Nicodaube/Grisp_robot/Laptop_controller/img/arrow.png

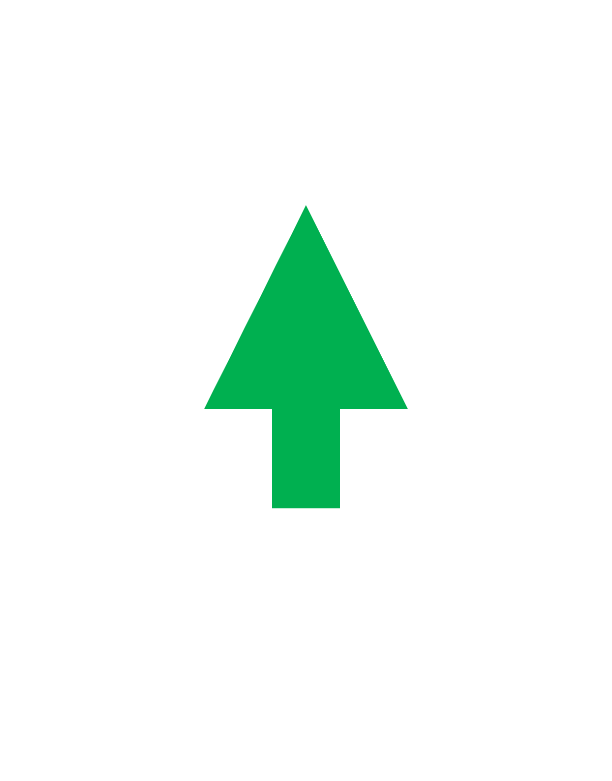
Laptop_controller/img/arrow.png
