Nicodaube/Grisp_robot/Laptop_controller/img/minus.png

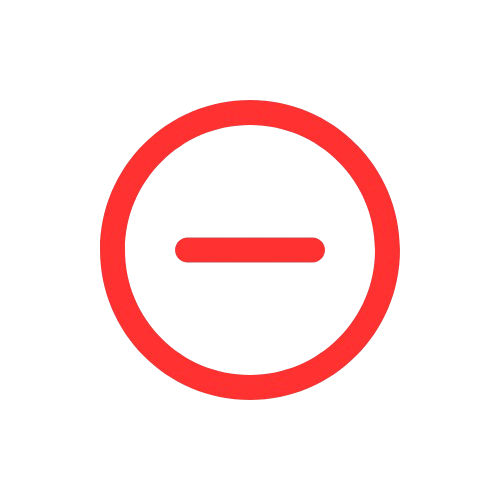
Laptop_controller/img/minus.png
