Nicodaube/Grisp_robot/Laptop_controller/img/plus.png

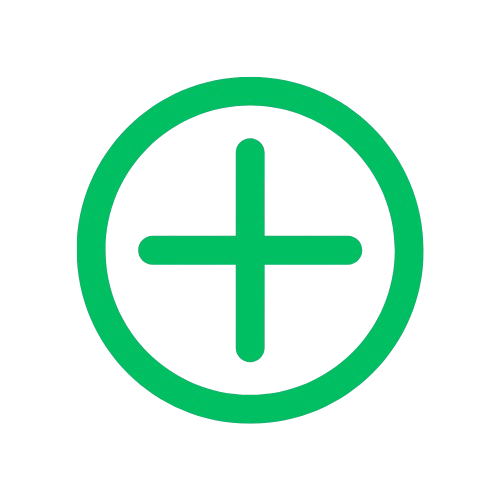
Laptop_controller/img/plus.png
