Nicodaube/Grisp_robot/Laptop_controller/img/Robot.png

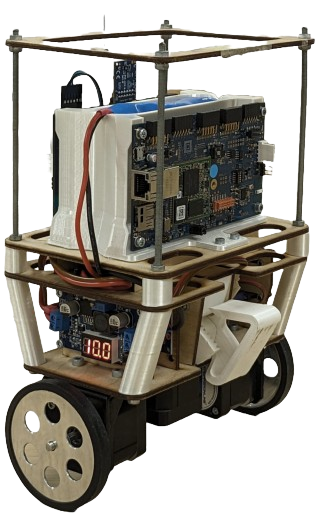
Laptop_controller/img/Robot.png
