Nicodaube/Grisp_robot/Laptop_controller/img/sensor.png

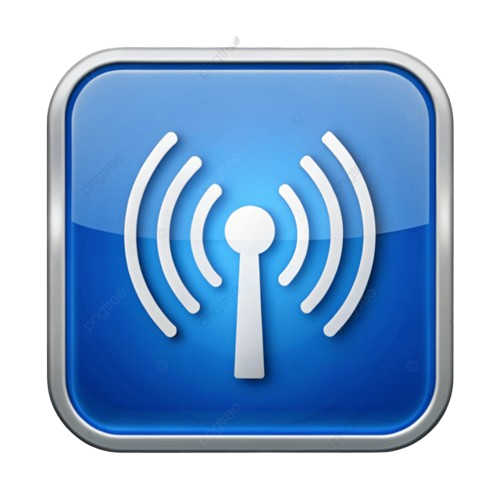
Laptop_controller/img/sensor.png
