Nicodaube/Grisp_robot/Laptop_controller/img/Stop_sign.png

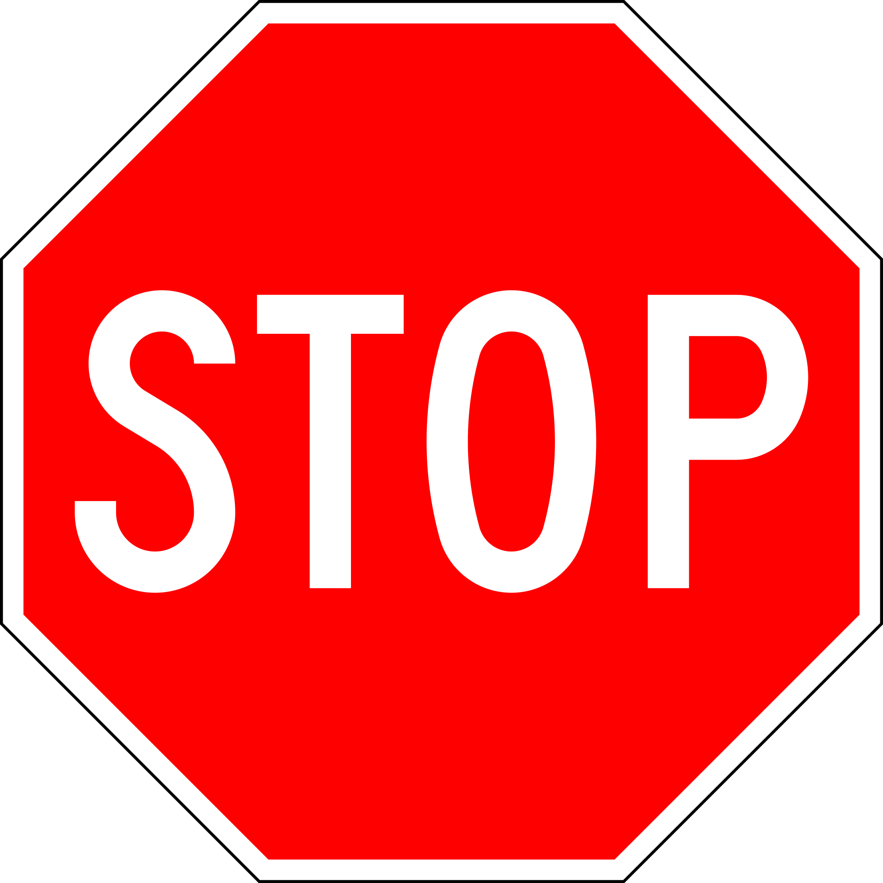
Laptop_controller/img/Stop_sign.png
