Nicodaube/Grisp_robot/Laptop_controller/img/zoom_in.png

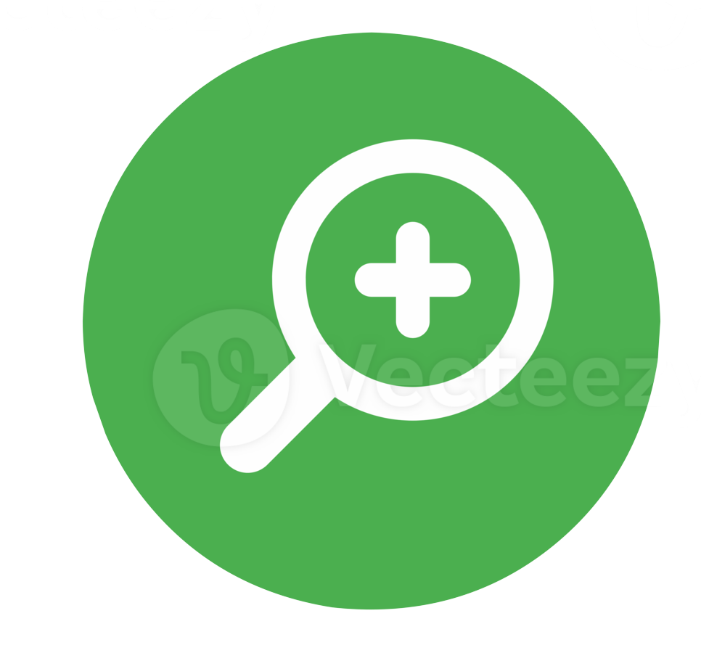
Laptop_controller/img/zoom_in.png
