Nicodaube/Grisp_robot/Laptop_controller/img/zoom_out.png

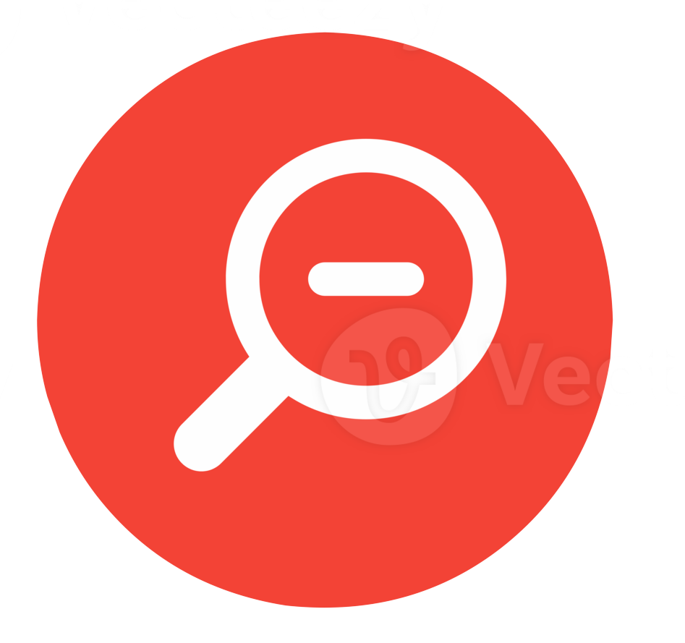
Laptop_controller/img/zoom_out.png
