Nicodaube/Grisp_robot/Wiki_images/GIFS/add_room.gif

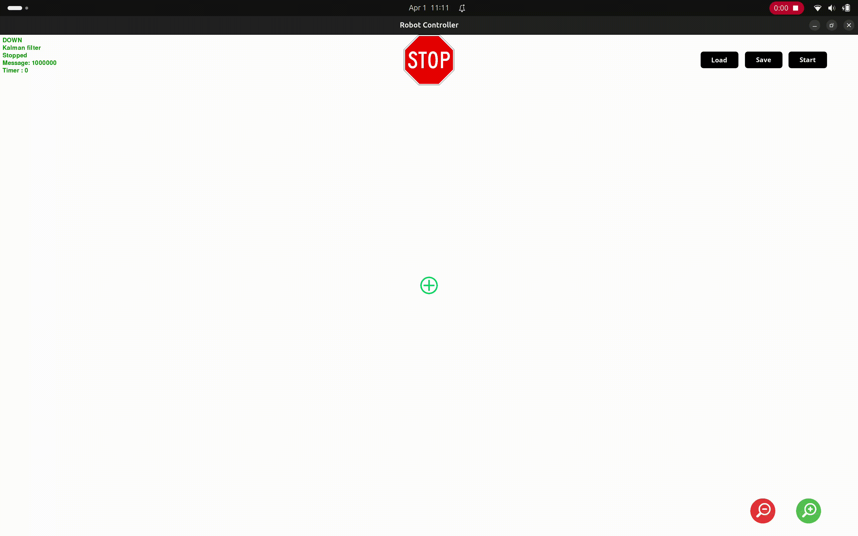
Wiki_images/GIFS/add_room.gif
