Nicodaube/Grisp_robot/Wiki_images/GIFS/add_sens.gif

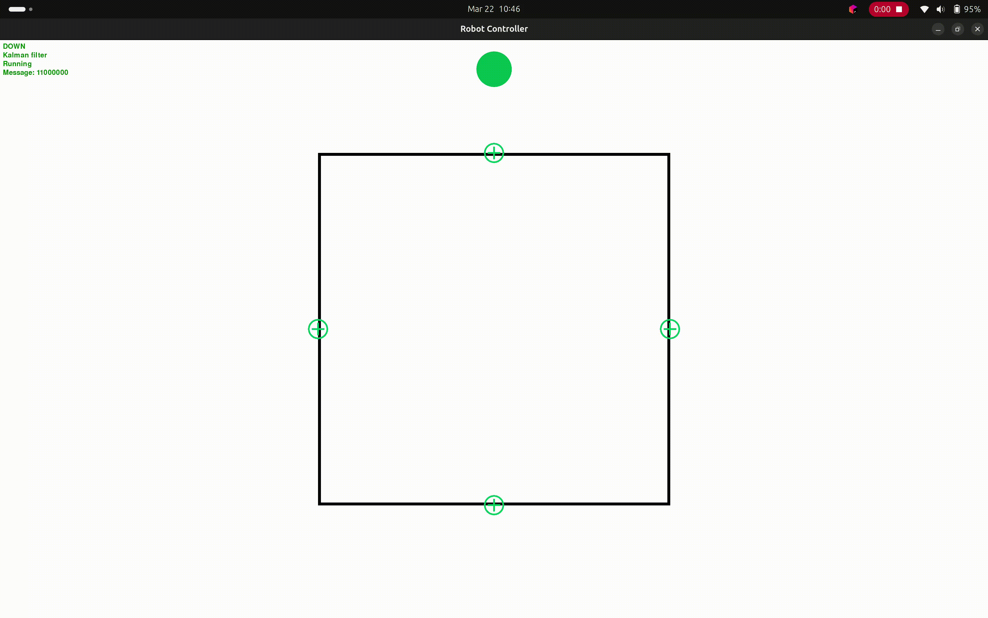
Wiki_images/GIFS/add_sens.gif
