Nicodaube/Grisp_robot/Wiki_images/GIFS/max_compat.gif

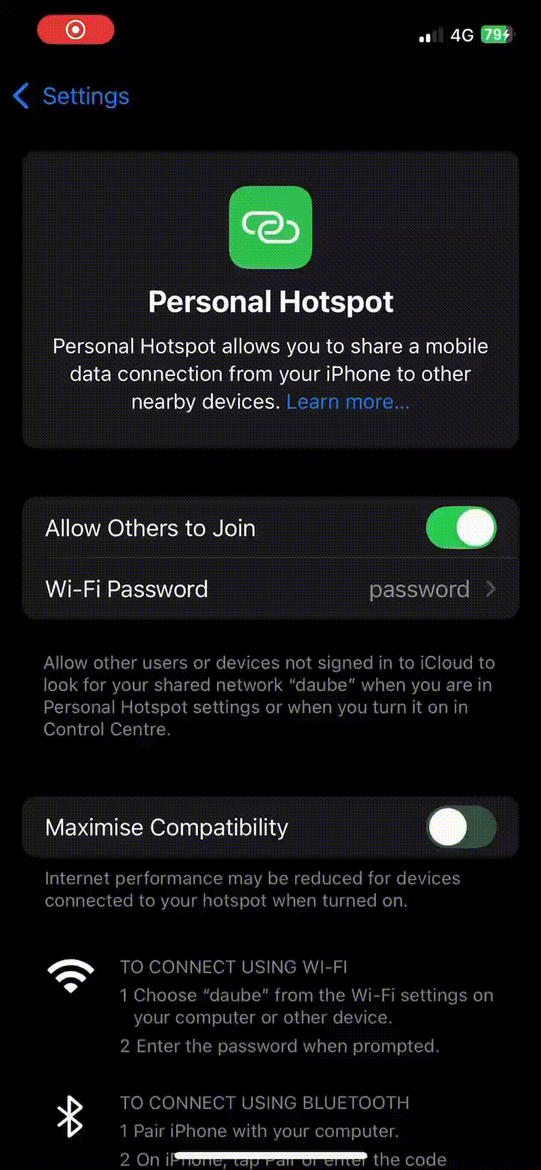
Wiki_images/GIFS/max_compat.gif
