Nicodaube/Grisp_robot/Wiki_images/GIFS/move_ctrl.gif

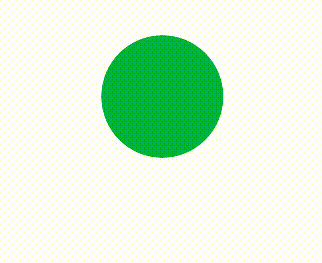
Wiki_images/GIFS/move_ctrl.gif
