Nicodaube/Grisp_robot/Wiki_images/img/jumpers.jpg

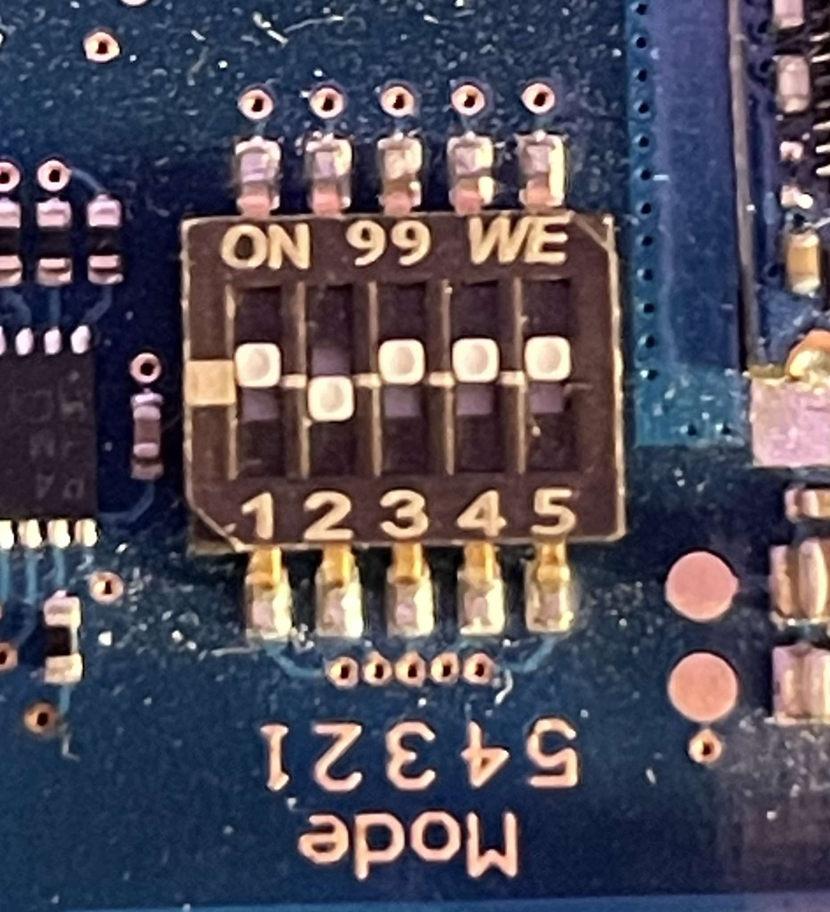
Wiki_images/img/jumpers.jpg
