Nicodaube/Grisp_robot/Wiki_images/img/motor_cables.png

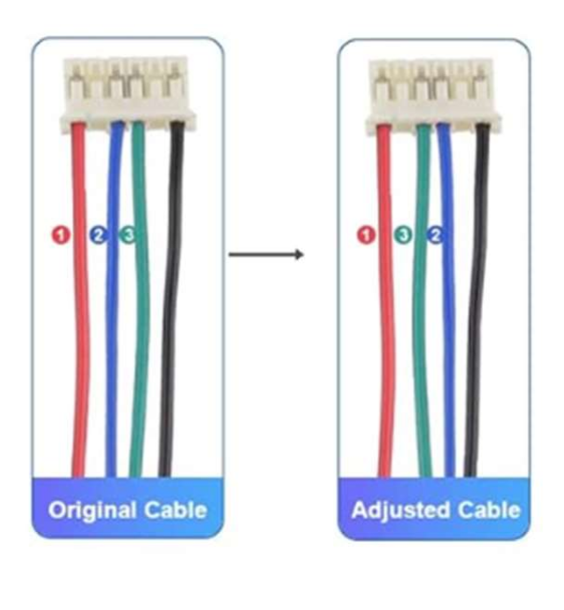
Wiki_images/img/motor_cables.png
