Nicodaube/Grisp_robot/Wiki_images/img/network_config.png

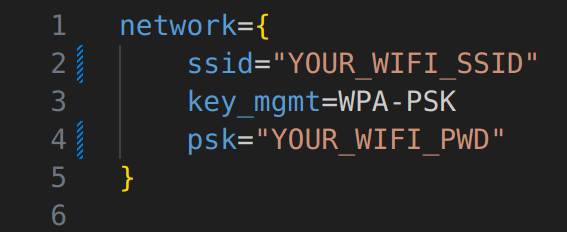
Wiki_images/img/network_config.png
