Nicodaube/Grisp_robot/Wiki_images/img/PCB.png

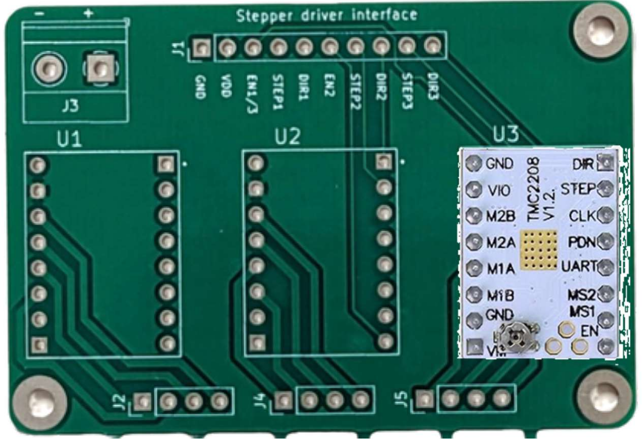
Wiki_images/img/PCB.png
