Nicodaube/Grisp_robot/Wiki_images/img/Sensor.jpeg

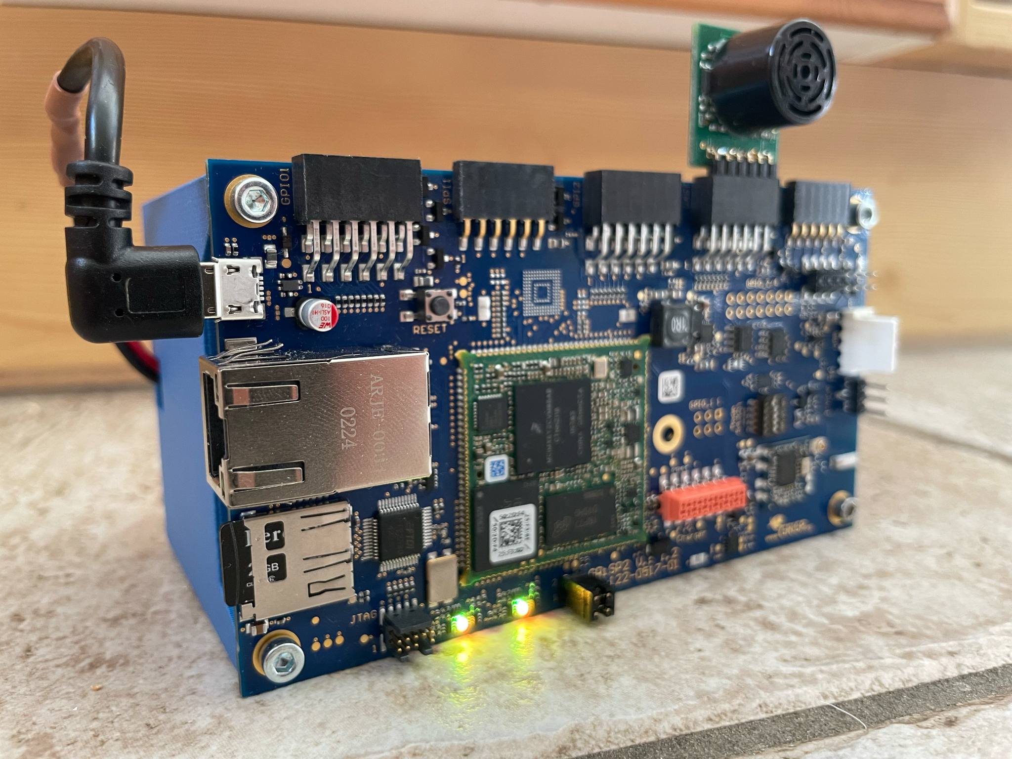
Wiki_images/img/Sensor.jpeg
