Nicodaube/Grisp_robot/Wiki_images/img/Sensor_FSM.png

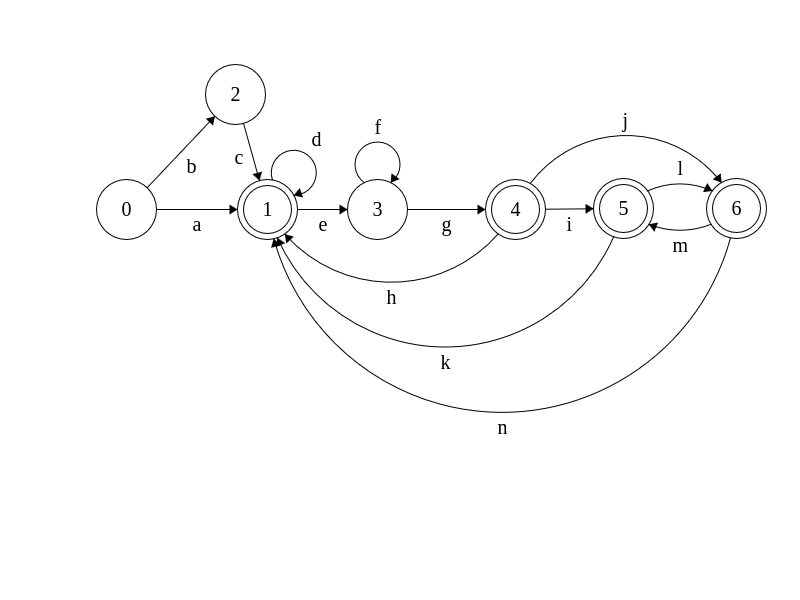
Wiki_images/img/Sensor_FSM.png
