Nicodaube/Grisp_robot/Hardware_robot/CAD_robot/Bevel_rack.SLDPRT

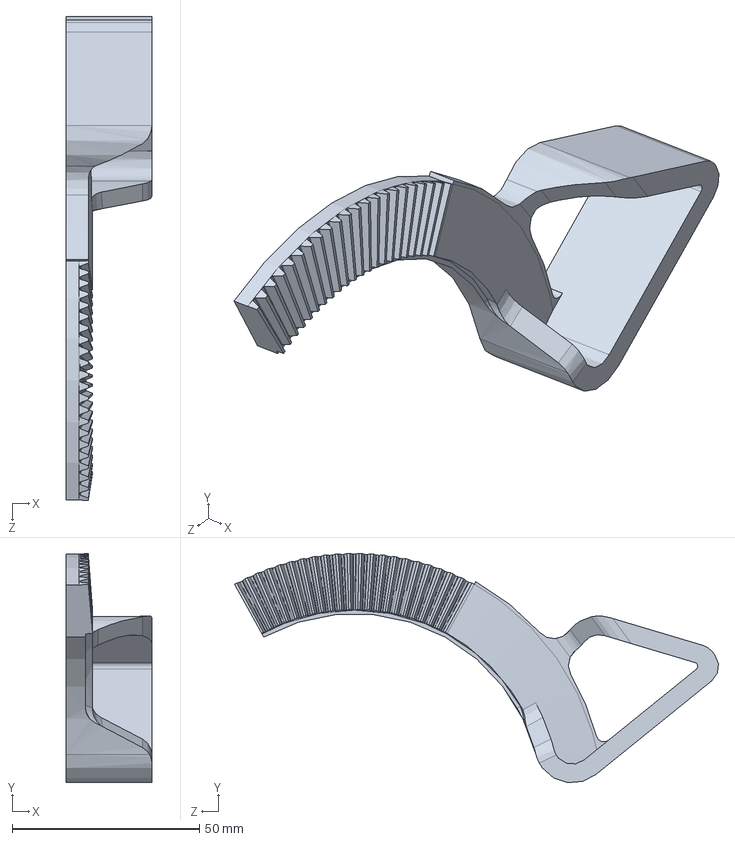
[picture p34: CAD file, 2025-02-24]
Hardware_robot/CAD_robot/Bevel_rack.SLDPRT
23.0 x 61.2 x 129.1 mm
