Nicodaube/Grisp_robot/Hardware_robot/Printing_files/3D/Dx2.STL

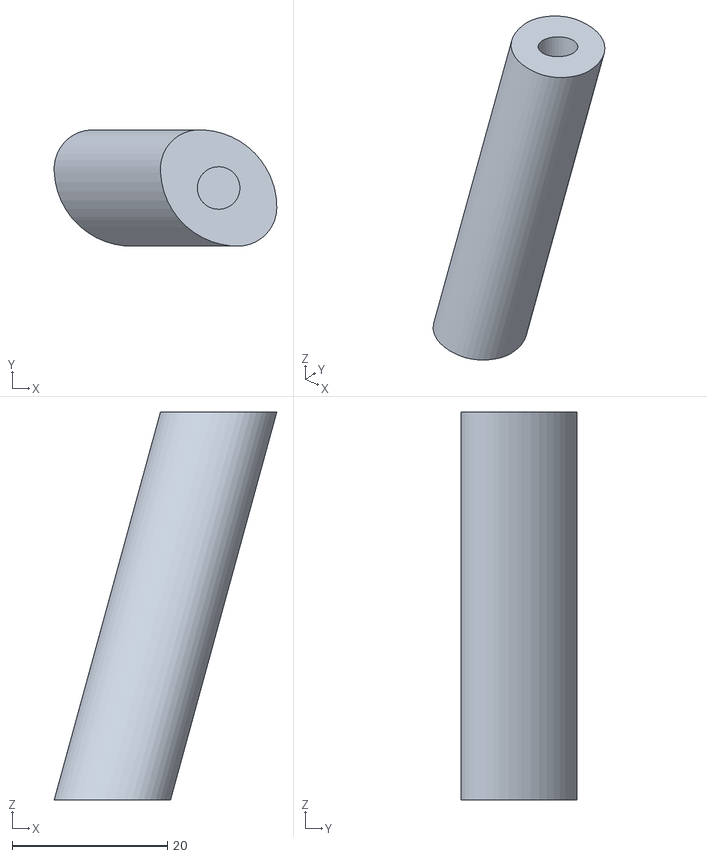
[picture p35: CAD file, 2025-02-23]
Hardware_robot/Printing_files/3D/Dx2.STL
28.7 x 15.0 x 50.0
