Nicodaube/Grisp_robot/Hardware_robot/Printing_files/Laser/H.dxf

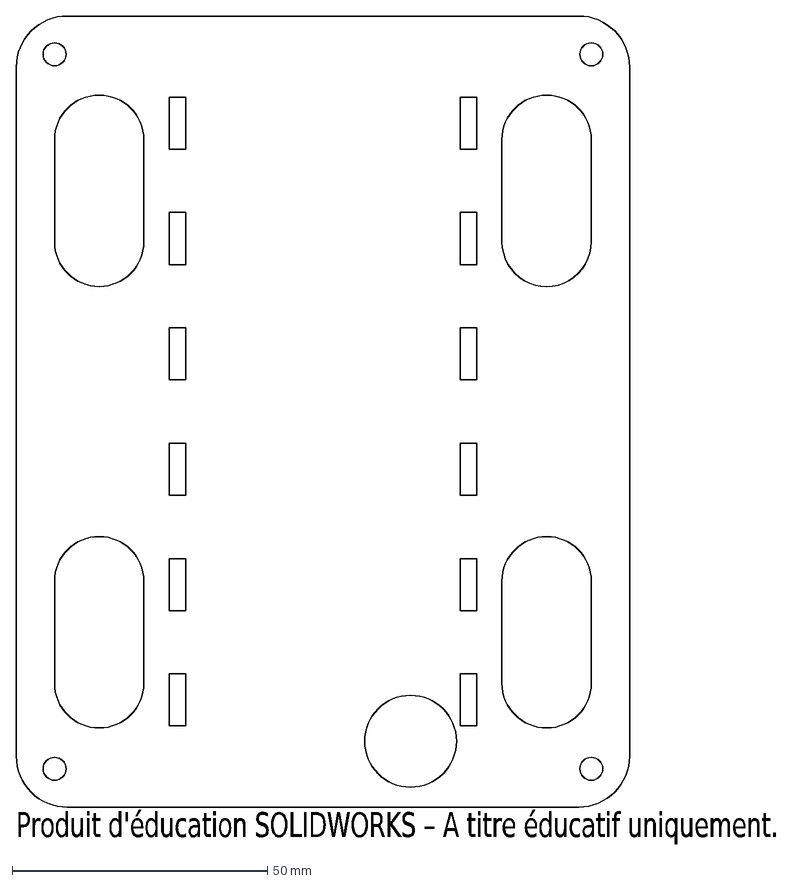
[picture p36: CAD file, 2025-02-23]
Hardware_robot/Printing_files/Laser/H.dxf
Produit d'éducation SOLIDWORKS – A titre éducatif uniquement.
