Nicodaube/Grisp_robot/Hardware_robot/TTGO LORA32 T3 V1.6.1/Wifi_Antenna.step

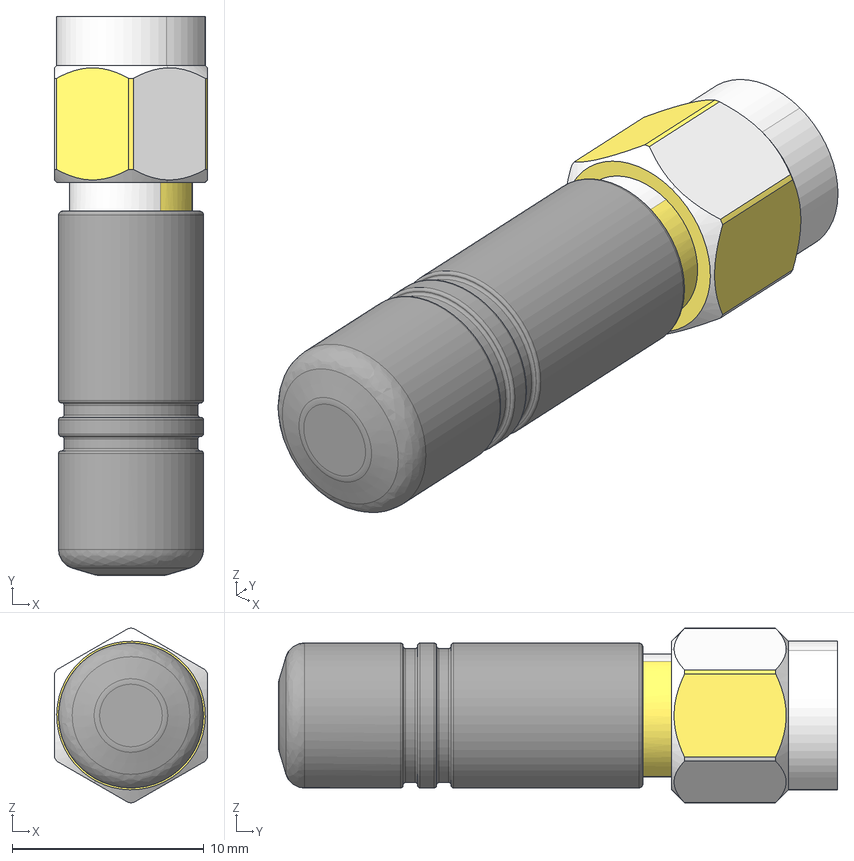
[picture p37: CAD file, 2025-02-24]
Hardware_robot/TTGO LORA32 T3 V1.6.1/Wifi_Antenna.step
8.00 x 29.2 x 9.10 mm
