Nicodaube/Grisp_robot/Hardware_Sensor/3D/Support coin_attache v2.stl

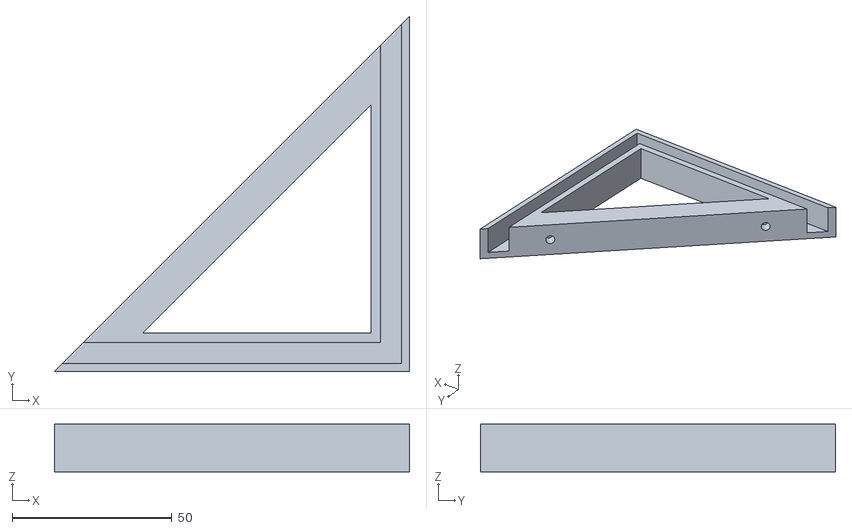
[picture p38: CAD file, 2025-04-22]
Hardware_Sensor/3D/Support coin_attache v2.stl
111.0 x 111.0 x 15.0
