Nicodaube/Grisp_robot/Hardware_robot/Printing_files/3D/G.STL

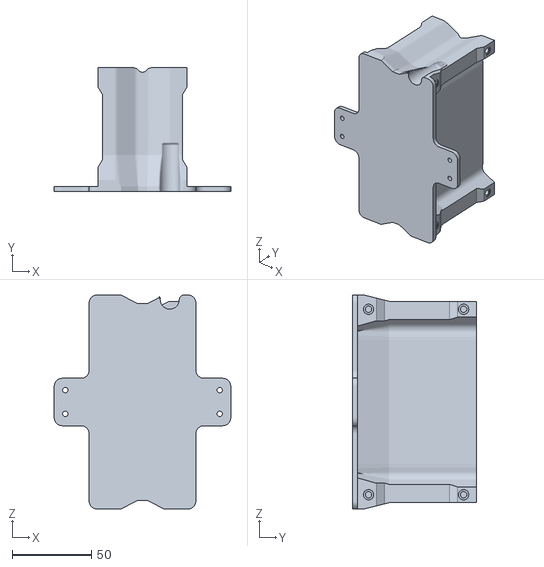
[picture p39: CAD file, 2025-02-23]
Hardware_robot/Printing_files/3D/G.STL
111.4 x 78.0 x 135.0
