Nicodaube/Grisp_robot/Hardware_robot/Printing_files/Laser/D.DXF

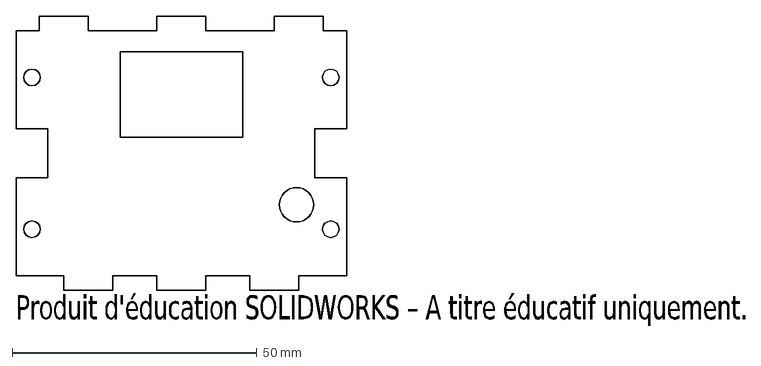
[picture p40: CAD file, 2025-02-23]
Hardware_robot/Printing_files/Laser/D.DXF
Produit d'éducation SOLIDWORKS – A titre éducatif uniquement.
