Nicodaube/Grisp_robot/Hardware_robot/TTGO LORA32 T3 V1.6.1/0603 Green.step

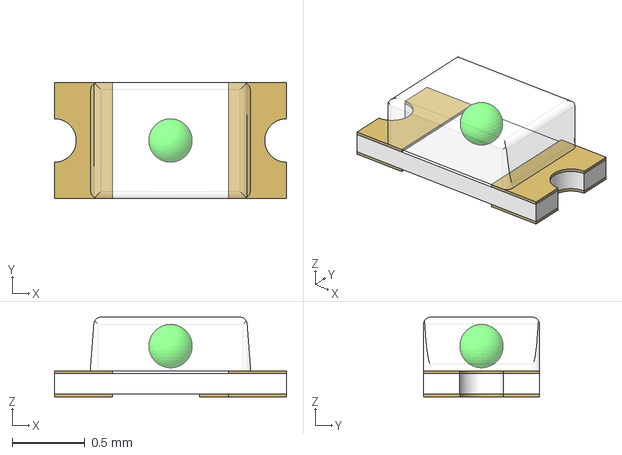
[picture p41: CAD file, 2025-02-24]
Hardware_robot/TTGO LORA32 T3 V1.6.1/0603 Green.step
1.60 x 0.8 x 0.55 mm
