Nicodaube/Grisp_robot/Hardware_robot/CAD_robot/BatteryPackBlue.SLDPRT

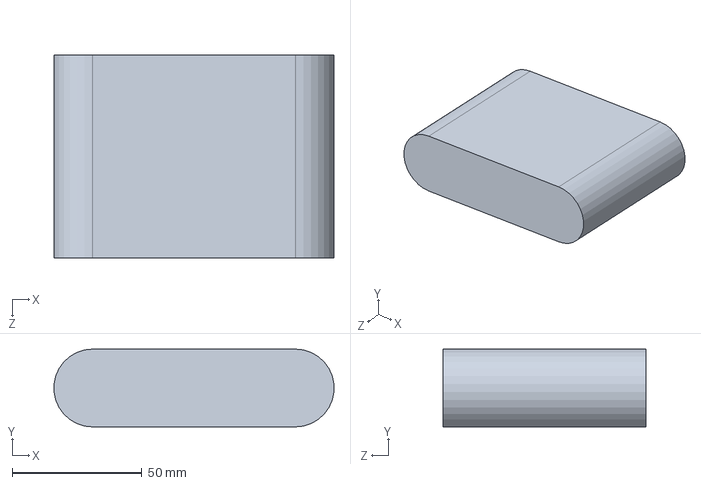
[picture p42: CAD file, 2025-02-24]
Hardware_robot/CAD_robot/BatteryPackBlue.SLDPRT
107.8 x 30.0 x 78.0 mm
