Nicodaube/Grisp_robot/Hardware_robot/Printing_files/3D/B.STL

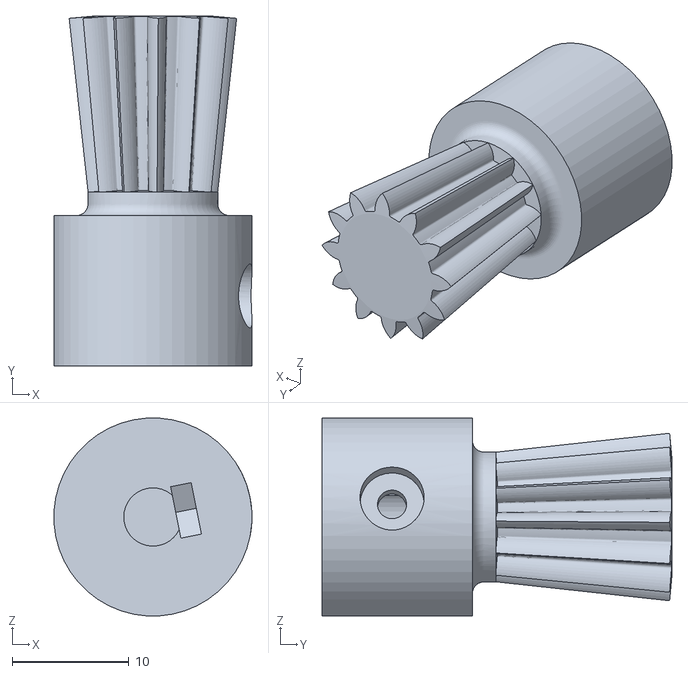
[picture p43: CAD file, 2025-02-23]
Hardware_robot/Printing_files/3D/B.STL
17.0 x 30.0 x 17.0
