Nicodaube/Grisp_robot/Hardware_robot/Printing_files/Laser/C.dxf

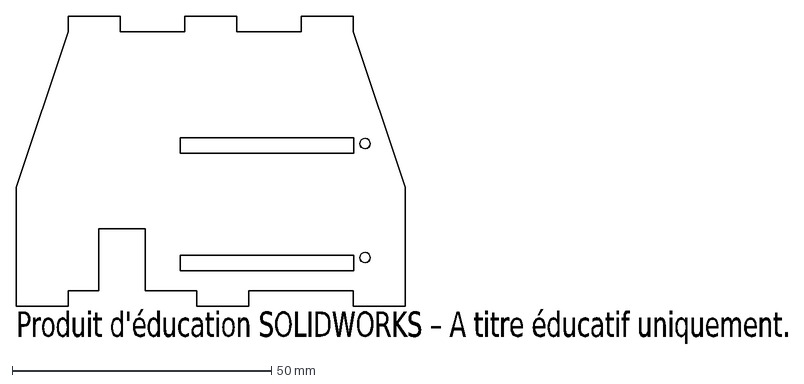
[picture p44: CAD file, 2025-02-23]
Hardware_robot/Printing_files/Laser/C.dxf
Produit d'éducation SOLIDWORKS – A titre éducatif uniquement.
