Nicodaube/Grisp_robot/Hardware_robot/Printing_files/3D/Hx2.STL

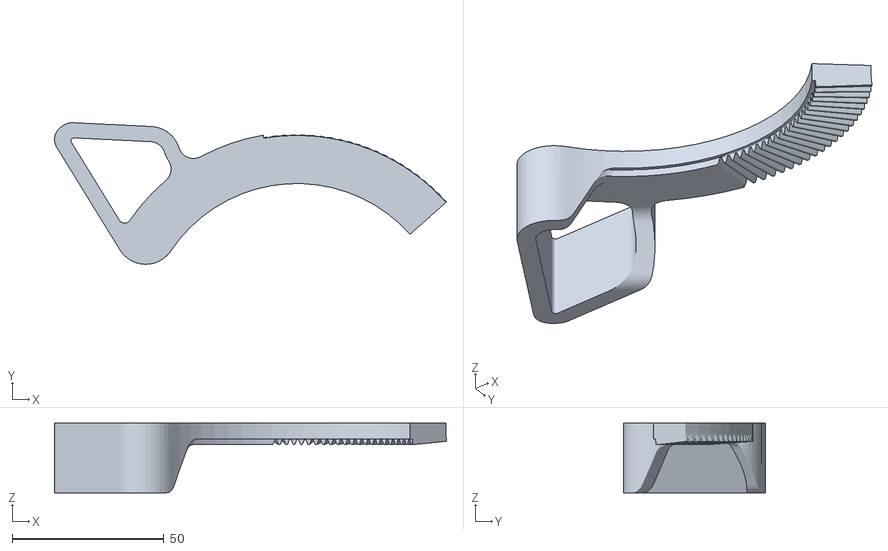
[picture p45: CAD file, 2025-02-23]
Hardware_robot/Printing_files/3D/Hx2.STL
129.4 x 46.8 x 23.0
