Nicodaube/Grisp_robot/Hardware_robot/Printing_files/Laser/Bx2.dxf

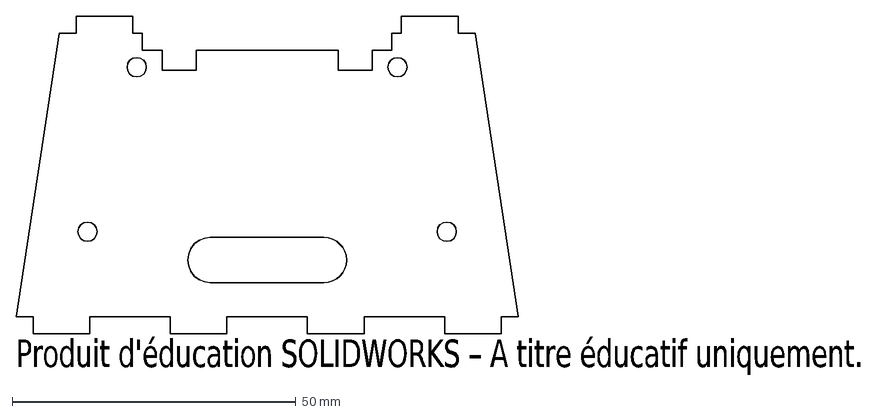
[picture p46: CAD file, 2025-02-23]
Hardware_robot/Printing_files/Laser/Bx2.dxf
Produit d'éducation SOLIDWORKS – A titre éducatif uniquement.
