Nicodaube/Grisp_robot/Hardware_robot/TTGO LORA32 T3 V1.6.1/1TS003B.step

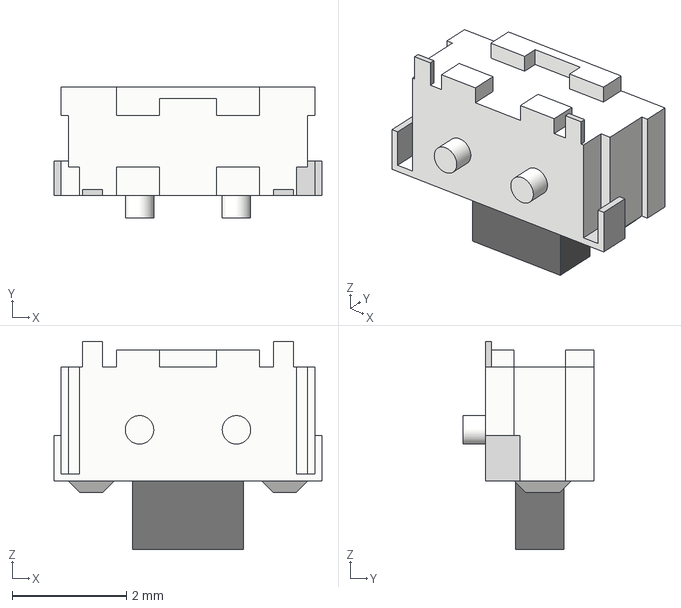
[picture p47: CAD file, 2025-02-24]
Hardware_robot/TTGO LORA32 T3 V1.6.1/1TS003B.step
4.70 x 2.30 x 3.65 mm
