Nicodaube/Grisp_robot/Hardware_robot/Printing_files/Laser/A.dxf

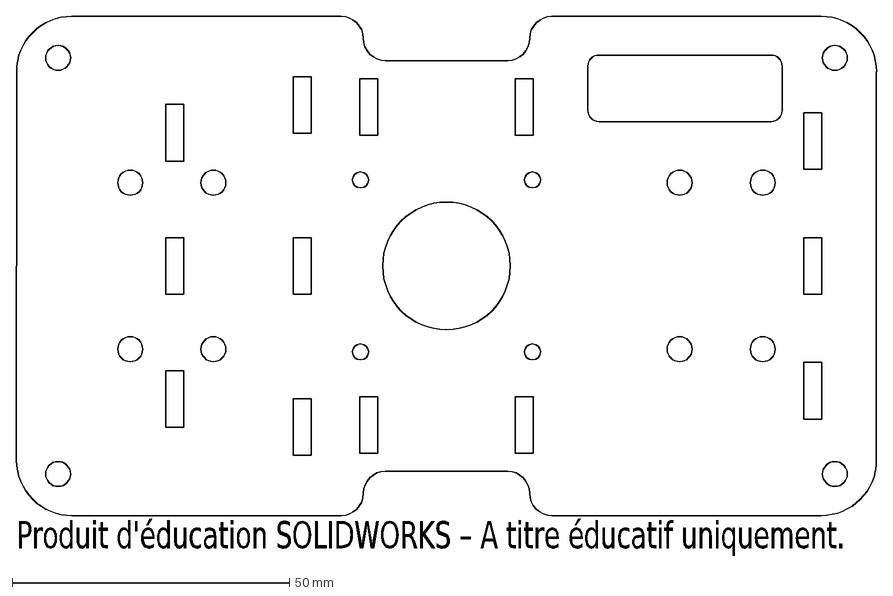
[picture p48: CAD file, 2025-02-23]
Hardware_robot/Printing_files/Laser/A.dxf
Produit d'éducation SOLIDWORKS – A titre éducatif uniquement.
