Nicodaube/Grisp_robot/Hardware_robot/CAD_robot/Pièce20.SLDPRT

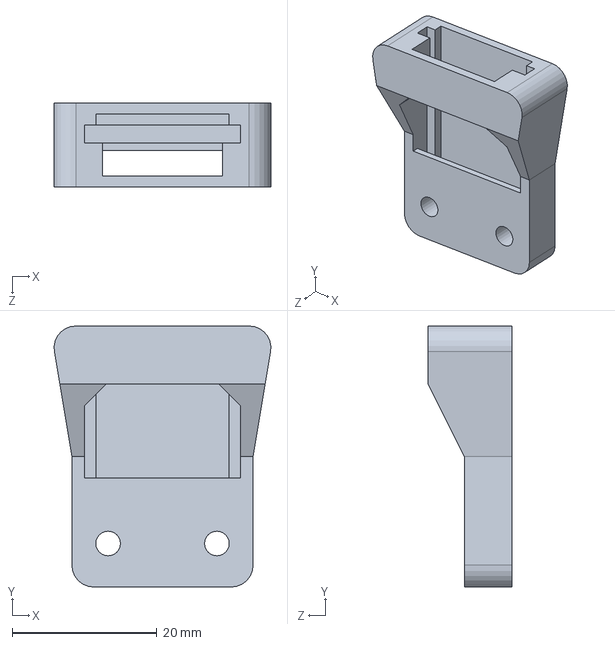
[picture p49: CAD file, 2025-02-24]
Hardware_robot/CAD_robot/Pièce20.SLDPRT
29.9 x 36.0 x 11.6 mm
