Nicodaube/Grisp_robot/Hardware_robot/Printing_files/3D/C.STL

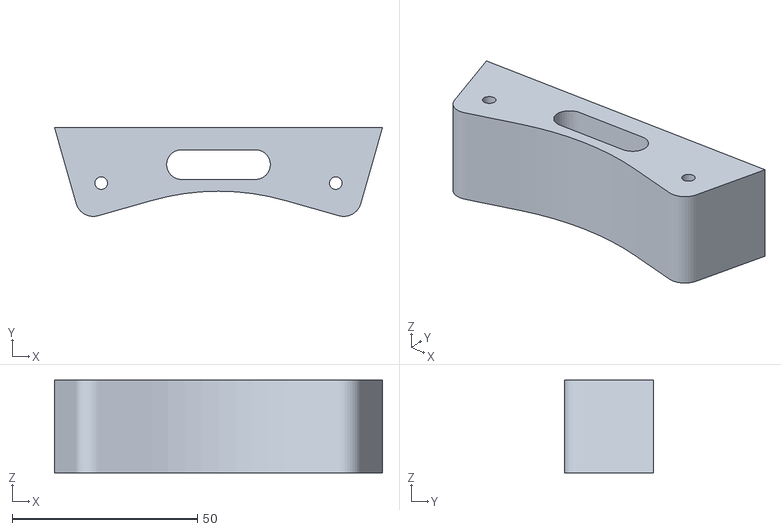
[picture p50: CAD file, 2025-02-23]
Hardware_robot/Printing_files/3D/C.STL
88.6 x 24.0 x 25.0
