Nicodaube/Grisp_robot/Hardware_robot/Printing_files/Laser/Gx2.DXF

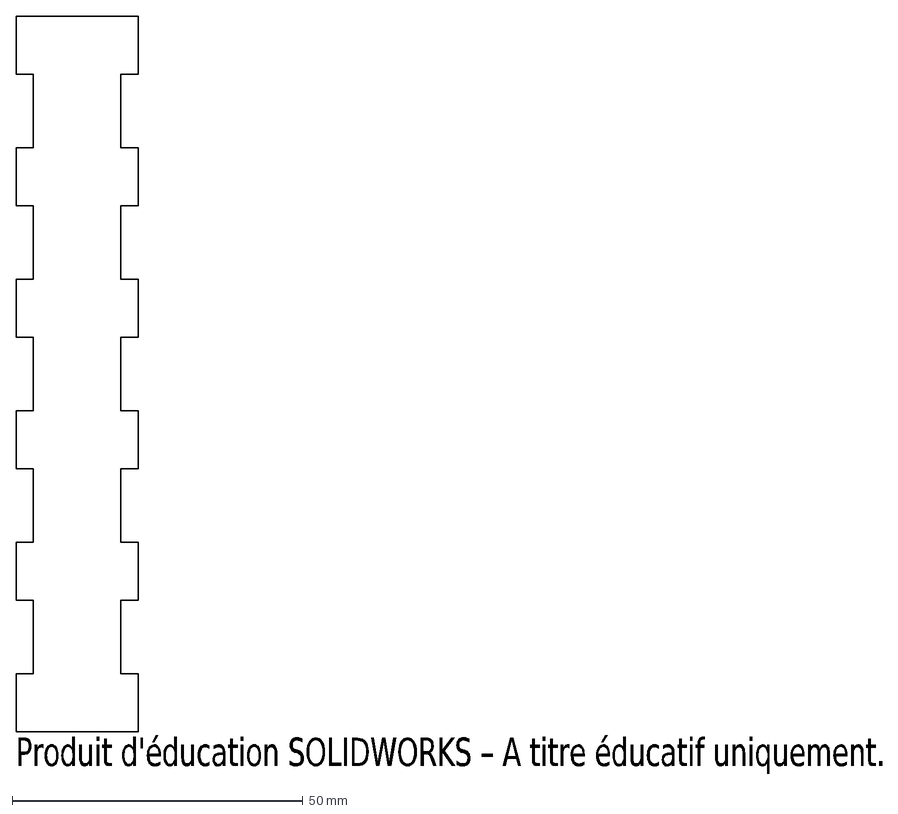
[picture p51: CAD file, 2025-02-23]
Hardware_robot/Printing_files/Laser/Gx2.DXF
Produit d'éducation SOLIDWORKS – A titre éducatif uniquement.
