Nicodaube/Grisp_robot/Hardware_robot/TTGO LORA32 T3 V1.6.1/ESP32-S3-QFN56-77-44.SLDPRT

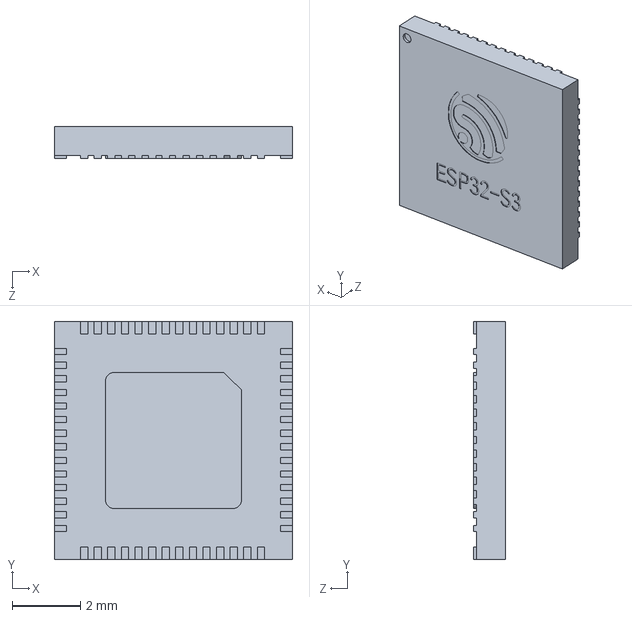
[picture p52: CAD file, 2025-02-24]
Hardware_robot/TTGO LORA32 T3 V1.6.1/ESP32-S3-QFN56-77-44.SLDPRT
7.00 x 7.00 x 0.95 mm
