Nicodaube/Grisp_robot/Hardware_robot/Printing_files/Laser/I.DXF

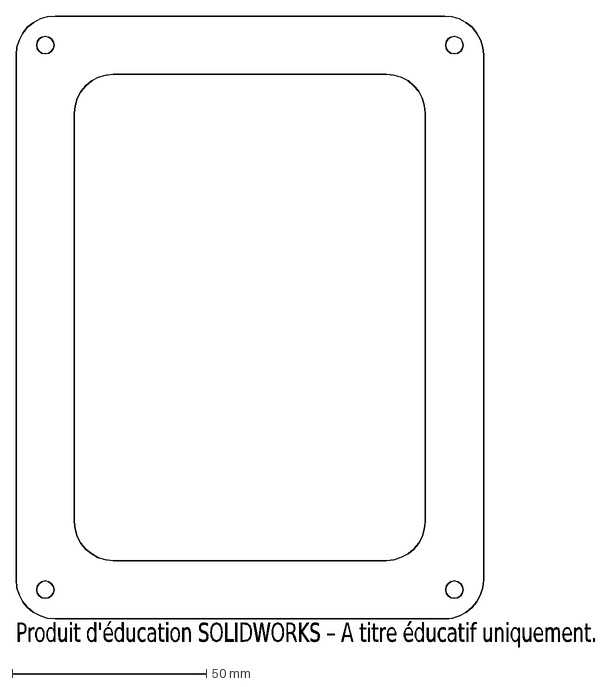
[picture p53: CAD file, 2025-02-23]
Hardware_robot/Printing_files/Laser/I.DXF
Produit d'éducation SOLIDWORKS – A titre éducatif uniquement.
