Nicodaube/Grisp_robot/Hardware_robot/TTGO LORA32 T3 V1.6.1/SMA-angled.SLDPRT

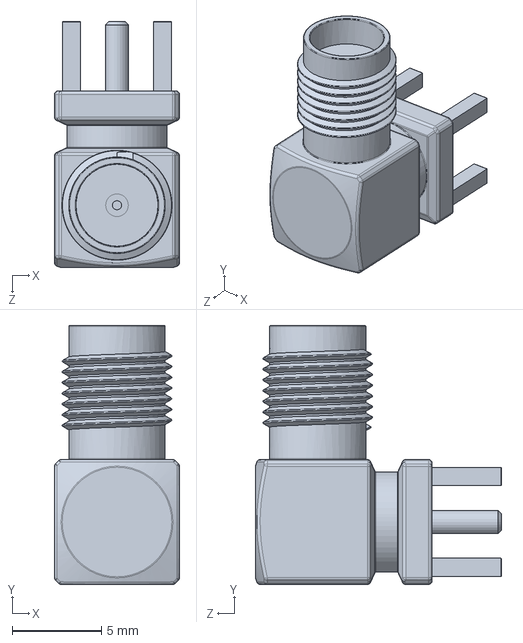
[picture p54: CAD file, 2025-02-24]
Hardware_robot/TTGO LORA32 T3 V1.6.1/SMA-angled.SLDPRT
7.00 x 14.5 x 13.8 mm
