Nicodaube/Grisp_robot/Hardware_robot/TTGO LORA32 T3 V1.6.1/ANT1, PRO-OB-440, M5Stamp-C3.SLDPRT

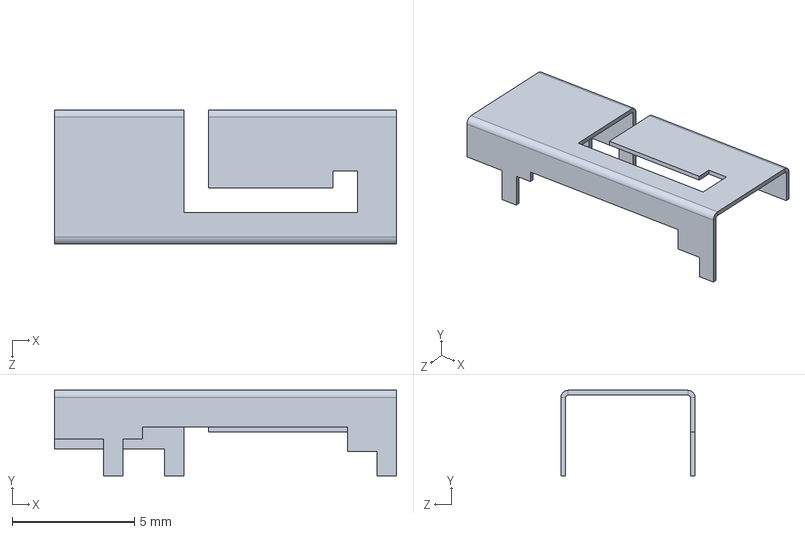
[picture p55: CAD file, 2025-02-24]
Hardware_robot/TTGO LORA32 T3 V1.6.1/ANT1, PRO-OB-440, M5Stamp-C3.SLDPRT
14.0 x 3.50 x 5.50 mm
