Nicodaube/Grisp_robot/Hardware_robot/TTGO LORA32 T3 V1.6.1/PZ_Switch_SMD.stp

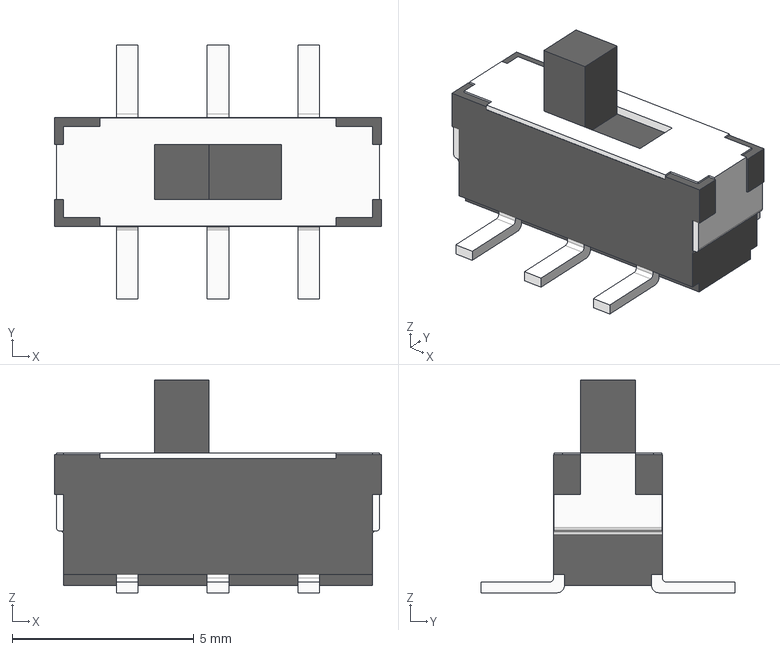
[picture p56: CAD file, 2025-02-24]
Hardware_robot/TTGO LORA32 T3 V1.6.1/PZ_Switch_SMD.stp
9.00 x 7.00 x 5.85 mm
