Nicodaube/Grisp_robot/Hardware_robot/TTGO LORA32 T3 V1.6.1/u.Fl Antenna Connector - 523-A-1JB.SLDPRT

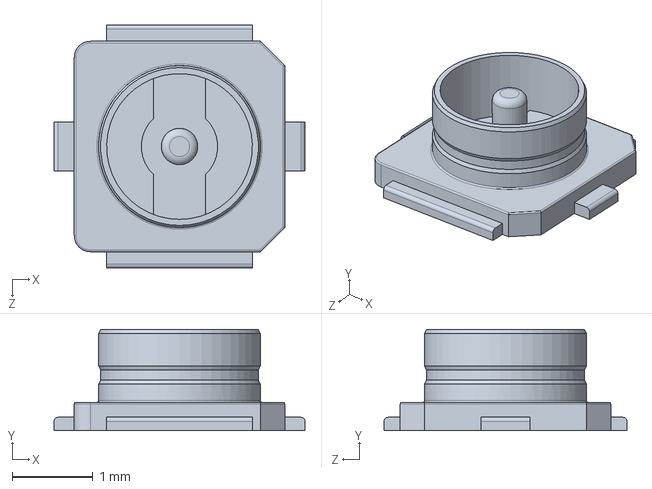
[picture p57: CAD file, 2025-02-24]
Hardware_robot/TTGO LORA32 T3 V1.6.1/u.Fl Antenna Connector - 523-A-1JB.SLDPRT
3.10 x 1.25 x 3.00 mm
