Nicodaube/Grisp_robot/Hardware_robot/TTGO LORA32 T3 V1.6.1/Micro USB-B Female 5Pin SMD.STEP

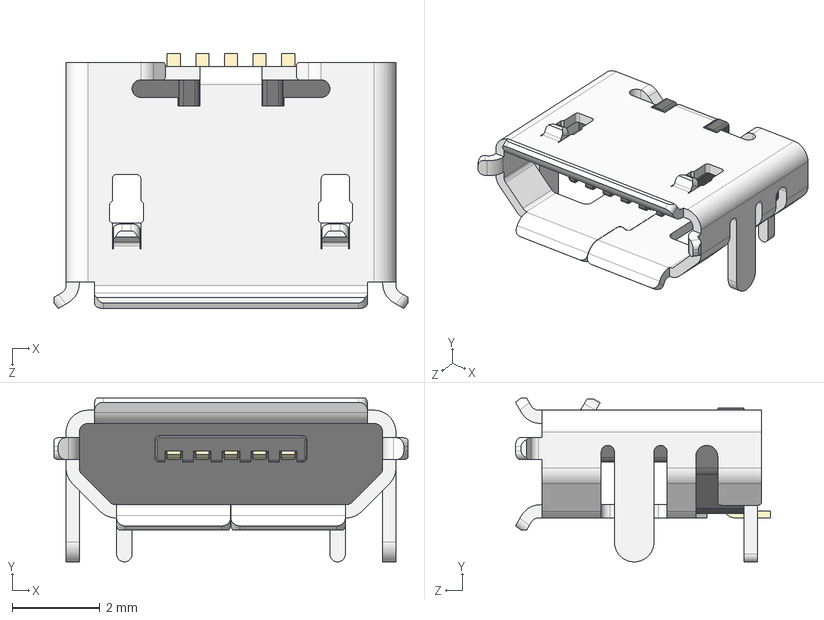
[picture p58: CAD file, 2025-02-24]
Hardware_robot/TTGO LORA32 T3 V1.6.1/Micro USB-B Female 5Pin SMD.STEP
8.05 x 3.73 x 5.80 mm
