Nicodaube/Grisp_robot/Hardware_robot/TTGO LORA32 T3 V1.6.1/Micro SD Card.SLDPRT

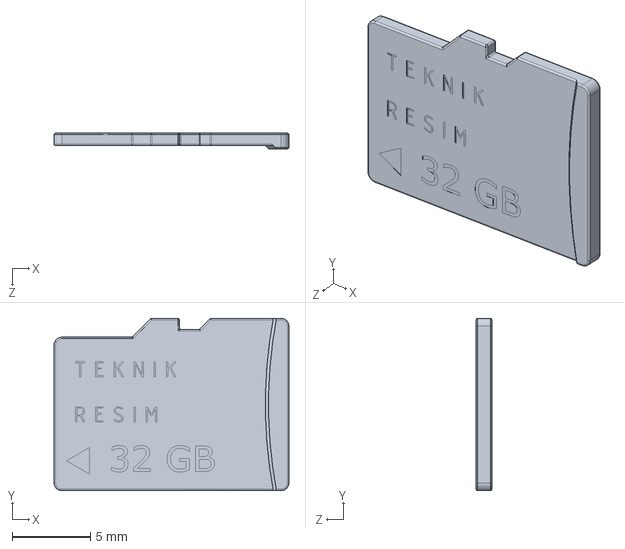
[picture p59: CAD file, 2025-02-24]
Hardware_robot/TTGO LORA32 T3 V1.6.1/Micro SD Card.SLDPRT
15.0 x 11.0 x 1.00 mm
