Nicodaube/Grisp_robot/Hardware_robot/TTGO LORA32 T3 V1.6.1/QFN24(4X4).SLDPRT

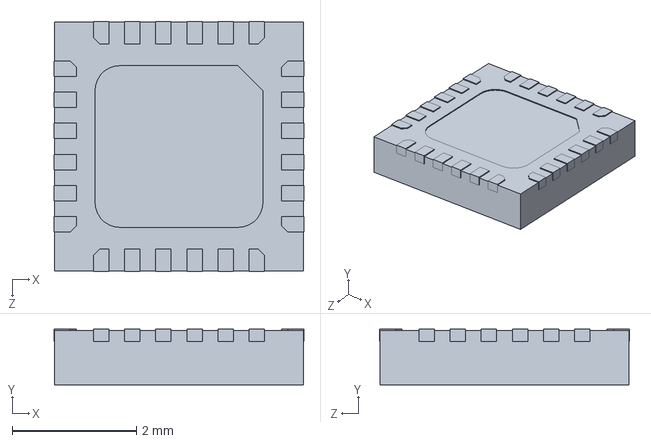
[picture p60: CAD file, 2025-02-24]
Hardware_robot/TTGO LORA32 T3 V1.6.1/QFN24(4X4).SLDPRT
4.02 x 0.9 x 4.02 mm
