Nicodaube/Grisp_robot/Hardware_robot/CAD_robot/17HE15-1504S.STEP

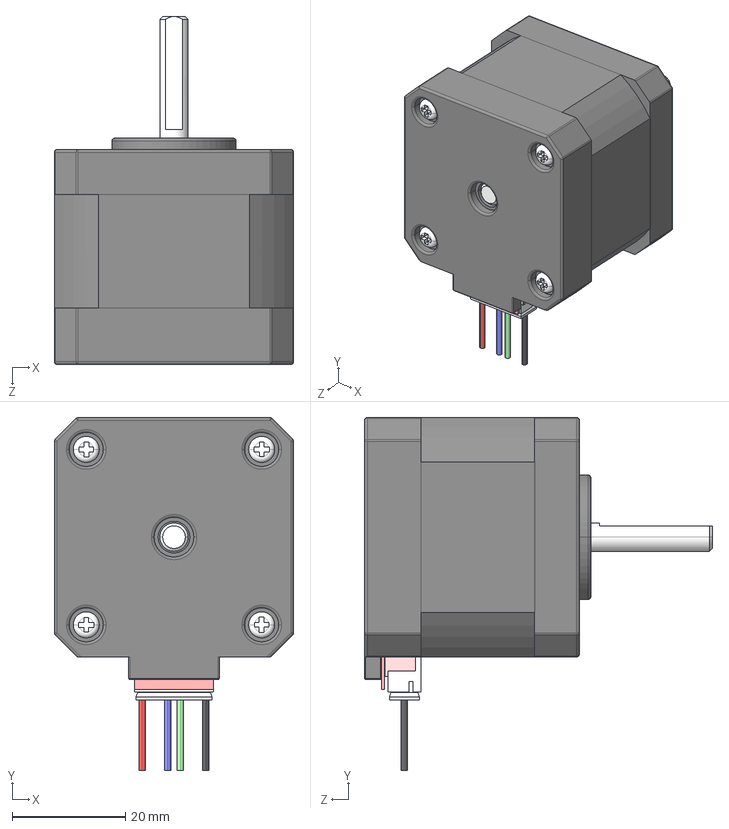
[picture p61: CAD file, 2025-02-24]
Hardware_robot/CAD_robot/17HE15-1504S.STEP
42.3 x 62.4 x 61.5 mm
