Nicodaube/Grisp_robot/Hardware_robot/TTGO LORA32 T3 V1.6.1/pcb lora.SLDPRT

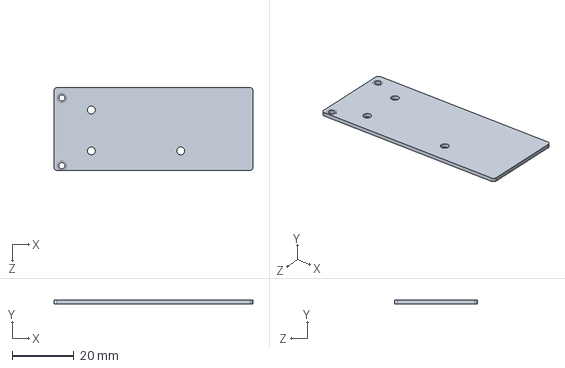
[picture p62: CAD file, 2025-02-24]
Hardware_robot/TTGO LORA32 T3 V1.6.1/pcb lora.SLDPRT
64.7 x 1.18 x 27.0 mm
