Nicodaube/Grisp_robot/Hardware_robot/TTGO LORA32 T3 V1.6.1/OLED block.SLDPRT

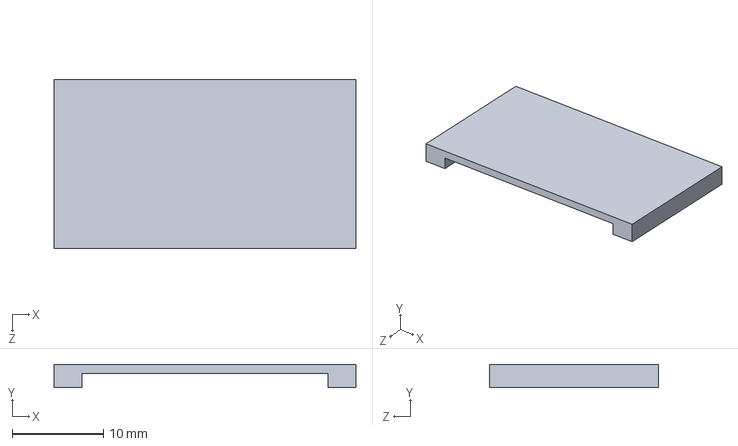
[picture p63: CAD file, 2025-02-24]
Hardware_robot/TTGO LORA32 T3 V1.6.1/OLED block.SLDPRT
33.1 x 2.55 x 18.5 mm
