Nicodaube/Grisp_robot/Hardware_robot/TTGO LORA32 T3 V1.6.1/RFM95 LoRa v15.step

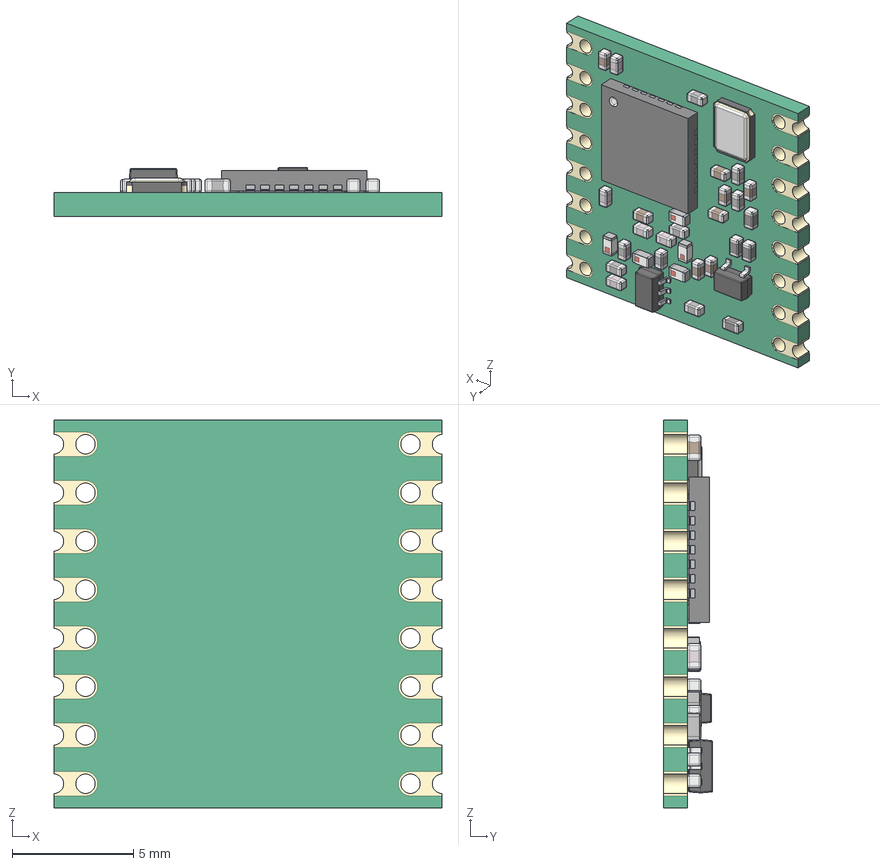
[picture p64: CAD file, 2025-02-24]
Hardware_robot/TTGO LORA32 T3 V1.6.1/RFM95 LoRa v15.step
16.0 x 2.04 x 16.0 mm
QFN 28
SMD Crystal
CAP 0403 x 8
CAP Ceramic 0403 x 8
Res 0403 x 4
CAP ML 0403 x 5
SOT-323
Inductor SMD 0403 x 5
SOT-363
