Nicodaube/Grisp_robot/Hardware_robot/TTGO LORA32 T3 V1.6.1/oled.SLDPRT

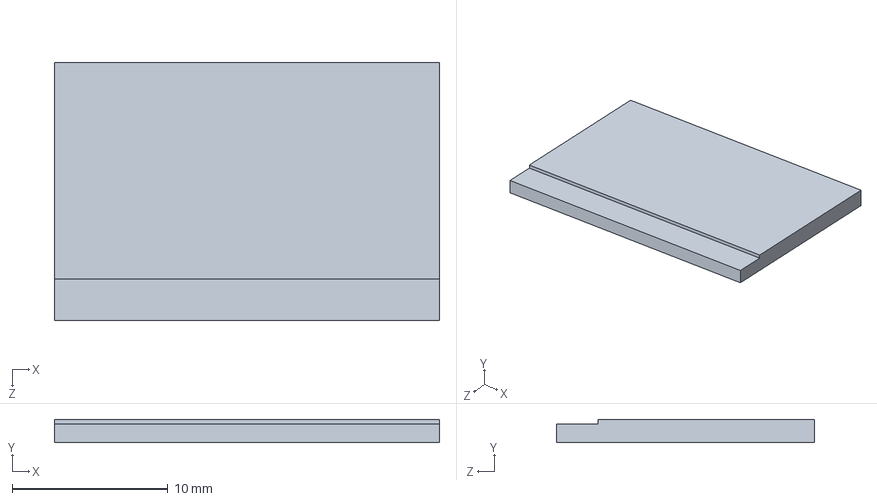
[picture p65: CAD file, 2025-02-24]
Hardware_robot/TTGO LORA32 T3 V1.6.1/oled.SLDPRT
24.7 x 1.50 x 16.6 mm
