Nicodaube/Grisp_robot/Hardware_robot/CAD_robot/BOOST.SLDPRT

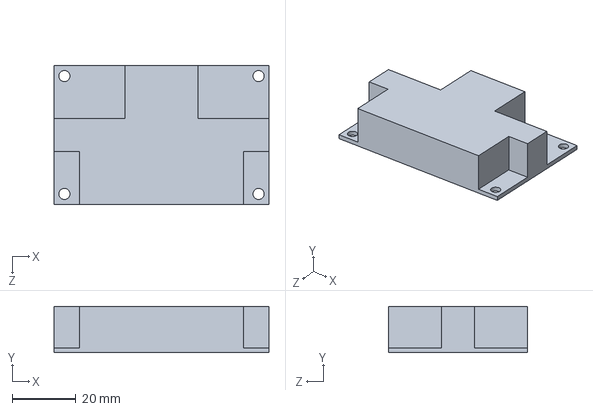
[picture p66: CAD file, 2025-02-24]
Hardware_robot/CAD_robot/BOOST.SLDPRT
67.5 x 14.5 x 43.5 mm
