Nicodaube/Grisp_robot/Hardware_robot/CAD_robot/GRiSP.SLDPRT

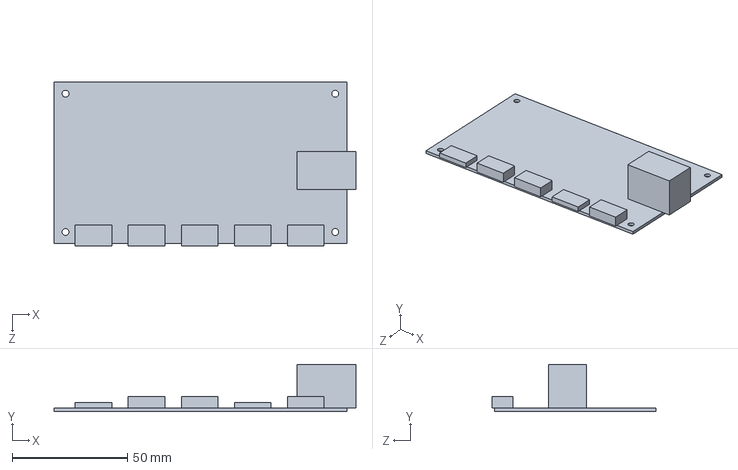
[picture p67: CAD file, 2025-02-24]
Hardware_robot/CAD_robot/GRiSP.SLDPRT
131.0 x 20.5 x 71.0 mm
