Nicodaube/Grisp_robot/Hardware_robot/CAD_robot/CN2596-2.stp

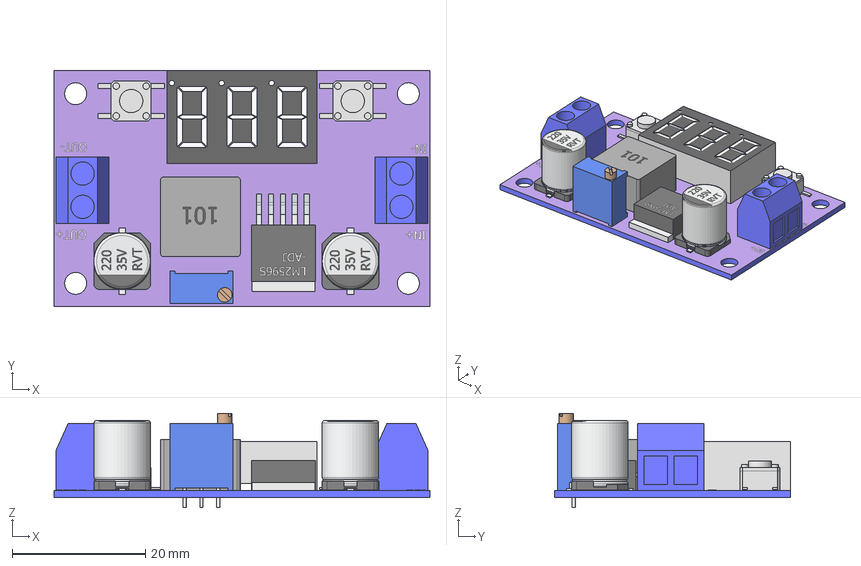
[picture p68: CAD file, 2025-02-24]
Hardware_robot/CAD_robot/CN2596-2.stp
56.5 x 35.5 x 14.2 mm
CN2596-2
LM2596S-ADJ
3631AH-6.8P
PZ_PushButton x 2
Trimpot_3296W
CAPAE-D8.0x10.2 x 2
