Nicodaube/Grisp_robot/Hardware_robot/CAD_robot/Rack_lat.SLDPRT

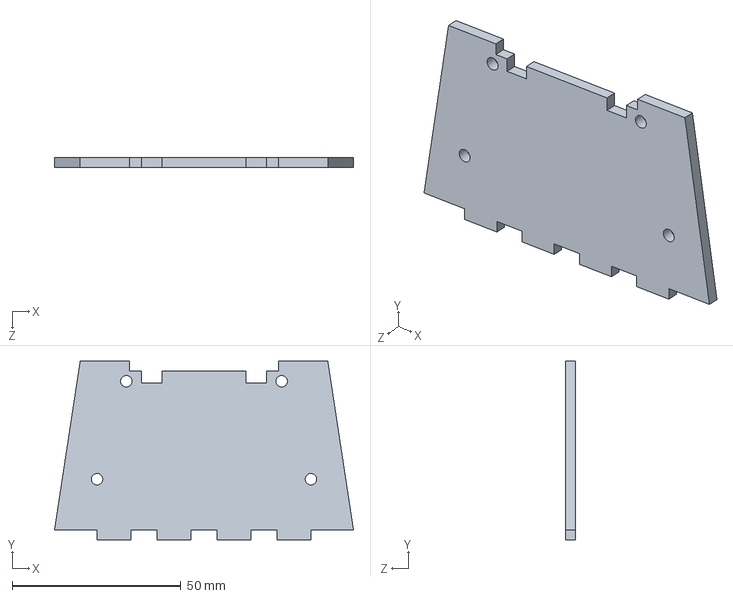
[picture p69: CAD file, 2025-02-24]
Hardware_robot/CAD_robot/Rack_lat.SLDPRT
88.6 x 53.0 x 3.00 mm
