Nicodaube/Grisp_robot/Hardware_robot/CAD_robot/roue.SLDPRT

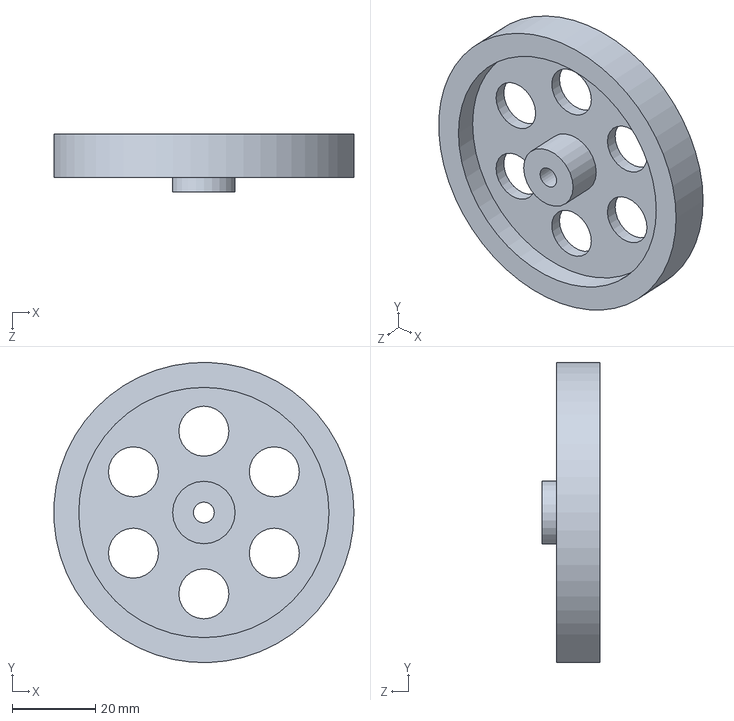
[picture p70: CAD file, 2025-02-24]
Hardware_robot/CAD_robot/roue.SLDPRT
71.9 x 72.0 x 14.0 mm
