Nicodaube/Grisp_robot/Hardware_robot/CAD_robot/battery_pack.SLDPRT

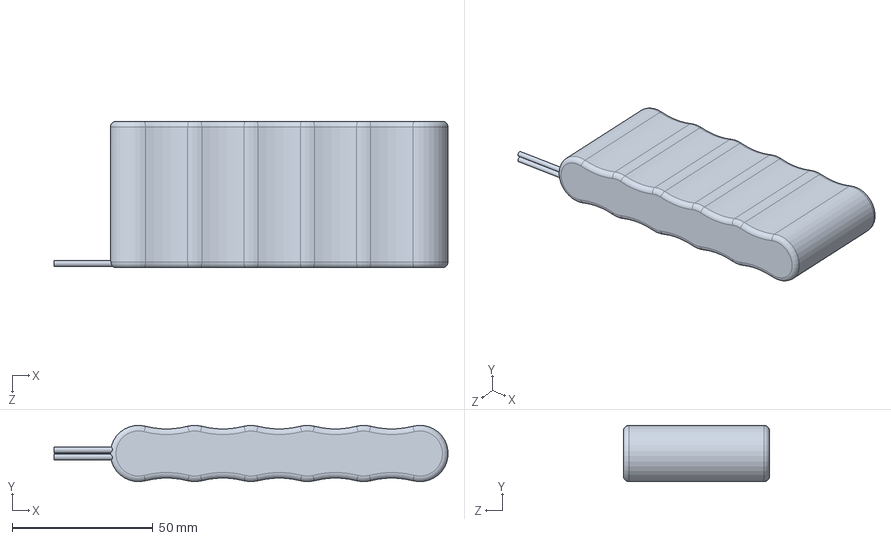
[picture p71: CAD file, 2025-02-24]
Hardware_robot/CAD_robot/battery_pack.SLDPRT
140.0 x 20.0 x 52.0 mm
