Nicodaube/Grisp_robot/Hardware_robot/CAD_robot/Support_stepper.SLDPRT

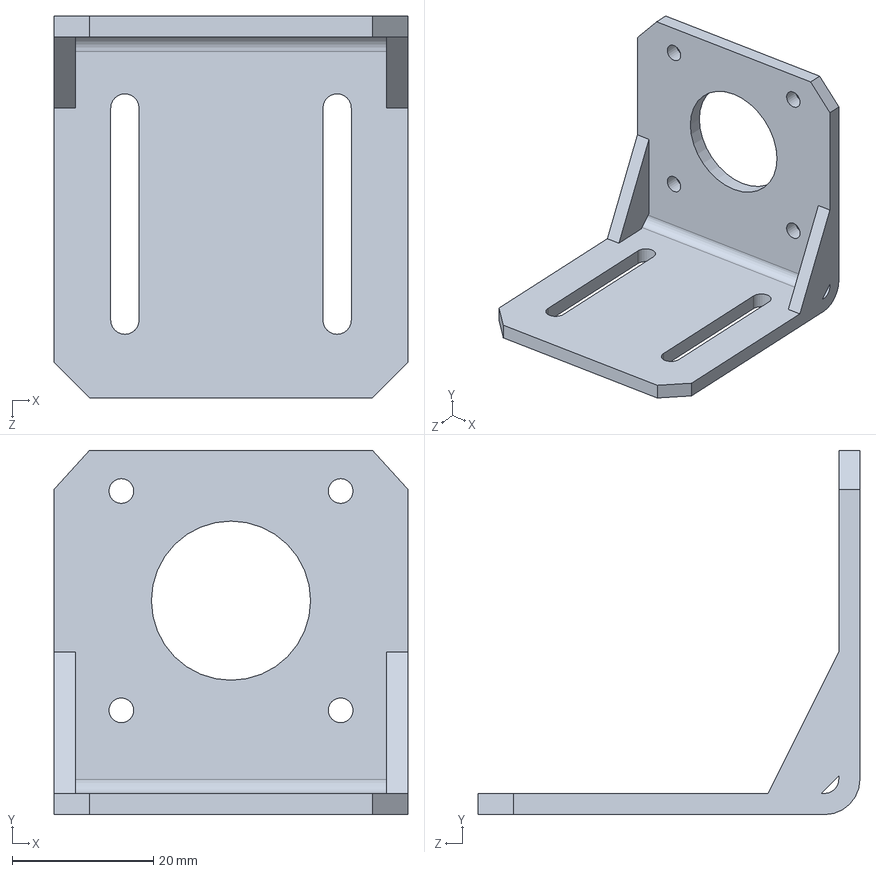
[picture p72: CAD file, 2025-02-24]
Hardware_robot/CAD_robot/Support_stepper.SLDPRT
50.0 x 51.5 x 54.0 mm
