Nicodaube/Grisp_robot/Laptop_controller/SaveParser.py

from Room import Room
import help_fun

def parse(filename, current_height, current_resize):
    rooms = []
    with open("./saves/" + filename, "r") as file:
        lines = file.readlines()
        resize = int(lines[0][16:])
        height = int(lines[1][9:])
        for line in lines[2:]:
            rooms.append(createRoom(line, height, current_height, resize, current_resize))
    return rooms


def createRoom(line, height, current_height, resize, current_resize):
    splitted = line.split(", ")
    new_width, new_height = help_fun.compute_current_size(int(splitted[0]), int(splitted[1]), height, current_height, resize, current_resize)
    room = Room(new_width,
                new_height,
                int(splitted[2][1:]),
                int(splitted[3][:-1]),
                int(splitted[4]))
    
    for side in ["L", "R", "T", "B"]:
        room.modify_side(side, "./img/plus.png", "plus")

    return room
